Rodvor/SmartKnob/src/ESP32/icons.h

#ifndef ICONS_H
#define ICONS_H

#include <pgmspace.h>

// All icons are 64x64 pixels, 1-bit bitmaps stored in PROGMEM.
// Draw with: tft.drawBitmap(ICON_X, ICON_Y, icon_xxx, ICON_W, ICON_H, TFT_WHITE);
// drawMenuIcon() is defined in ESP32.ino (not here) to avoid tft scope issues.

// Icons 96x96 made with https://notisrac.github.io/FileToCArray/

#define ICON_W 96
#define ICON_H 96
#define ICON_X 72   // (240 - 96) / 2
#define ICON_Y 65

#define SMALL_ICON_W 24
#define SMALL_ICON_H 24

#define UNMUTE_ID 0
#define MUTE_ID 1
#define DEAFEN_ID 2

#define VOLUME_COLOR 0xffff
#define DISCORD_COLOR 0x7bde
#define BRIGHT_COLOR 0xff97
#define MEDIA_COLOR 0xdaaa
#define BLUETOOTH_COLOR 0xc61f

#define UNMUTE_COLOR 0xbdf7
#define MUTE_COLOR 0xf800
#define DEAFEN_COLOR 0xf800

// ─────────────────────────────────────────────
// VOLUME ICON  (speaker with sound waves)
// ─────────────────────────────────────────────
const uint8_t icon_volume[] PROGMEM  = {
  0x00, 0x00, 0x00, 0x00, 0x00, 0x00, 0x00, 0x00, 0x00, 0x00, 0x00, 0x00, 
  0x00, 0x00, 0x00, 0x00, 0x00, 0x00, 0x00, 0x00, 0x00, 0x00, 0x00, 0x00, 
  0x00, 0x00, 0x00, 0x00, 0x00, 0x00, 0x00, 0x00, 0x00, 0x00, 0x00, 0x00, 
  0x00, 0x00, 0x00, 0x00, 0x00, 0x00, 0x00, 0x00, 0x00, 0x00, 0x00, 0x00, 
  0x00, 0x00, 0x00, 0x00, 0x00, 0x00, 0x00, 0x00, 0x00, 0x00, 0x00, 0x00, 
  0x00, 0x00, 0x00, 0x00, 0x00, 0x00, 0x00, 0x00, 0x00, 0x00, 0x00, 0x00, 
  0x00, 0x00, 0x00, 0x00, 0x00, 0x00, 0x00, 0x00, 0x00, 0x00, 0x00, 0x00, 
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
  0x70, 0x3e, 0x0f, 
  0x7c, 0x7c, 0x1f, 
  0x7e, 0xf8, 0xff, 
  0x7f, 0xf1, 0xfe, 
  0x7f, 0xe3, 0xfe, 
  0x7f, 0xc7, 0xfe, 
  0x3f, 0xa7, 0xfc, 
  0x1f, 0x77, 0xfc, 
  0x3e, 0xf7, 0xf8, 
  0x7d, 0xe7, 0xf0, 
  0xfb, 0xe7, 0xe0, 
  0xf1, 0x81, 0x80, 
  0x60, 0x00, 0x00
};





#endif // ICONS_H
