Rodvor/SmartKnob/src/ESP32/pin_config.h

#ifndef PIN_CONFIG_H
#define PIN_CONFIG_H

// SimpleFOC ports
#define EN 25
#define IN1 26
#define IN2 32
#define IN3 33

// AS5600 Encoder pins
#define ENCODER_SDA 21
#define ENCODER_SCL 22

// Touch
#define TP_SDA 19
#define TP_SCL 18
#define TP_INT 34
#define TP_RST 23

// Most screen configs in /Arduino/libraries/TFT_eSPI/User_Setup.h
#define BLK_PIN 2 // Screen on/off stuff

#endif
